jtulach/timing/boxes/StartGage02-Box_DsiplayCover_Part1.stl

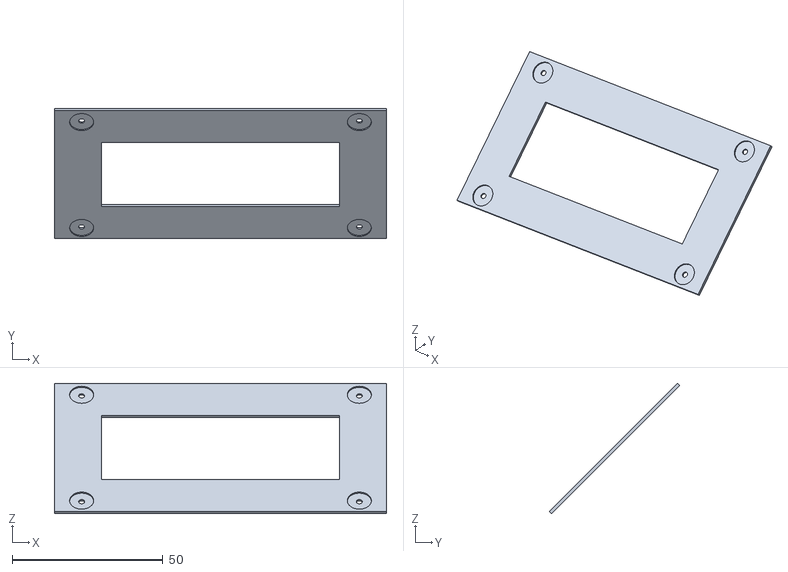
[picture p17: CAD file, 2019-12-12]
boxes/StartGage02-Box_DsiplayCover_Part1.stl
110.0 x 43.2 x 43.2
