jtulach/timing/boxes/krabickaSFotoTransistorem_04-Front1.stl

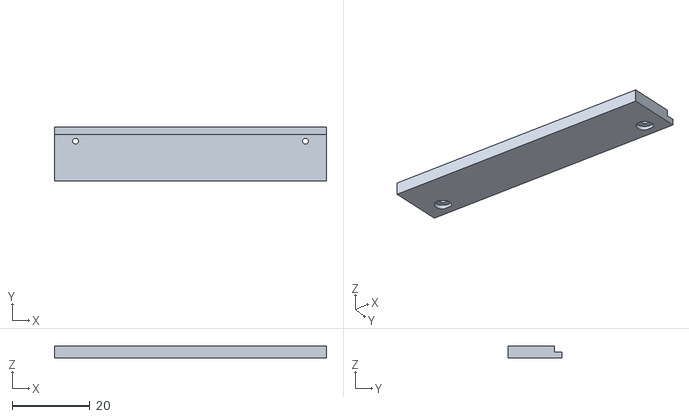
[picture p18: CAD file, 2019-12-12]
boxes/krabickaSFotoTransistorem_04-Front1.stl
70.0 x 14.0 x 3.00
