jtulach/timing/boxes/krabickaSFotoTransistorem_02-LaserHouse.stl

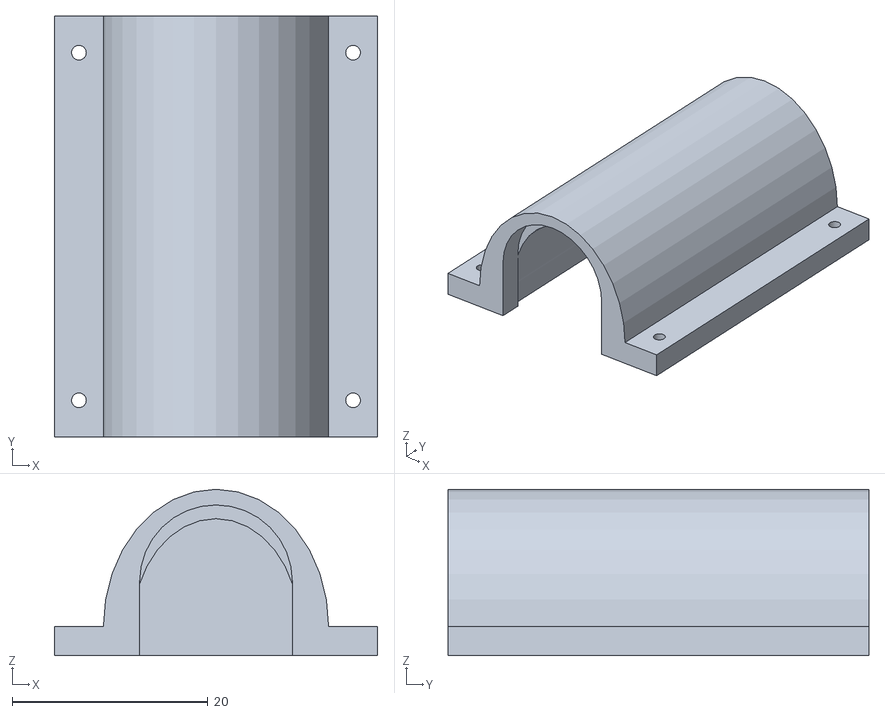
[picture p19: CAD file, 2019-12-12]
boxes/krabickaSFotoTransistorem_02-LaserHouse.stl
33.0 x 43.0 x 17.0
