jtulach/timing/boxes/krabickaSFotoTransistorem_04-Telescope_Part_2_Bottom.stl

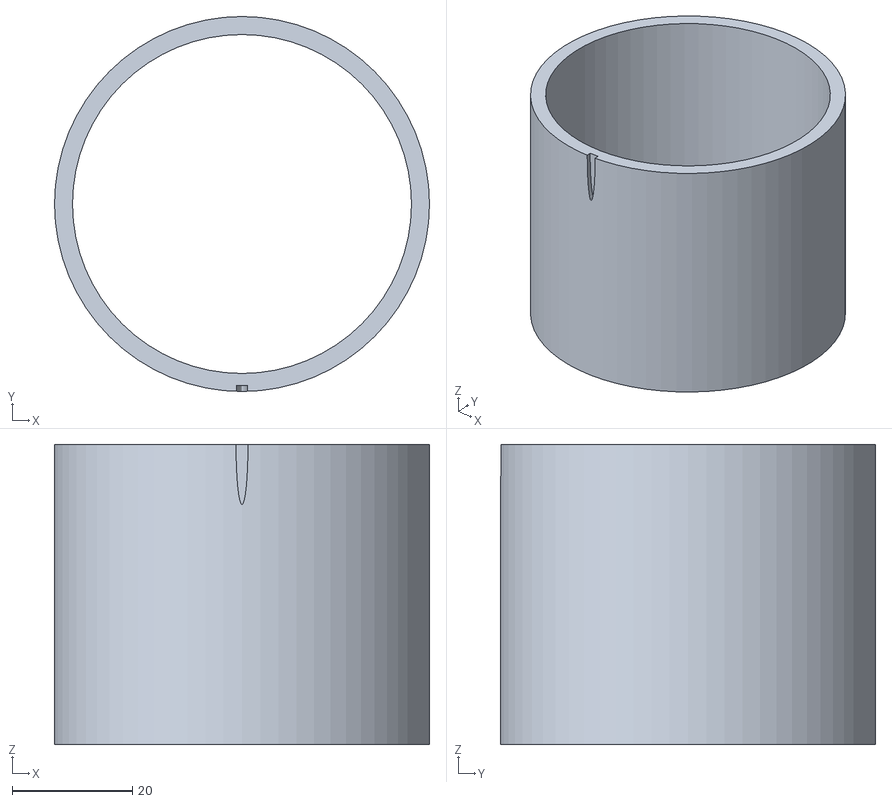
[picture p20: CAD file, 2019-12-12]
boxes/krabickaSFotoTransistorem_04-Telescope_Part_2_Bottom.stl
62.4 x 62.4 x 50.0
