jtulach/timing/boxes/krabickaSFotoTransistorem_04-Telescope_Part_5.stl

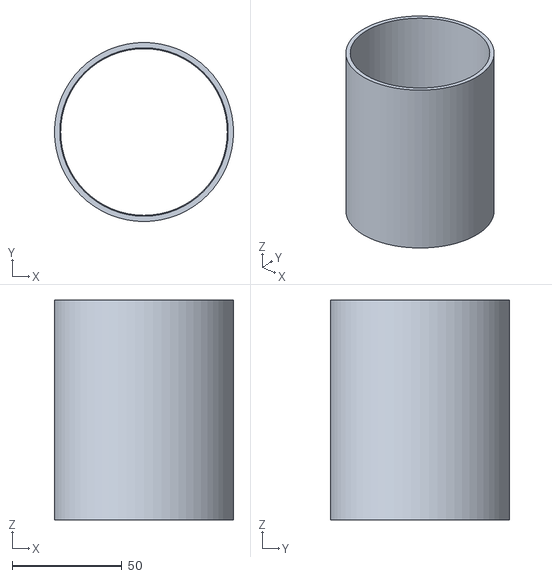
[picture p21: CAD file, 2019-12-12]
boxes/krabickaSFotoTransistorem_04-Telescope_Part_5.stl
81.4 x 81.4 x 100.0
