jtulach/timing/boxes/krabickaSFotoTransistorem_04-LaserBox_Right.stl

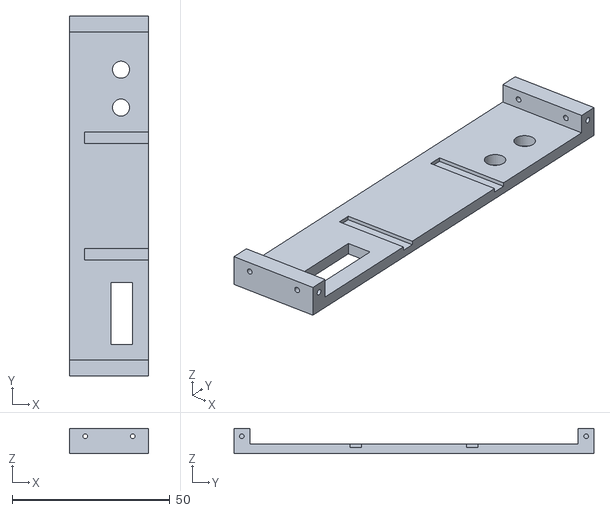
[picture p22: CAD file, 2019-12-12]
boxes/krabickaSFotoTransistorem_04-LaserBox_Right.stl
25.0 x 114.0 x 8.00
