jtulach/timing/boxes/StartGage02-RFISign.stl

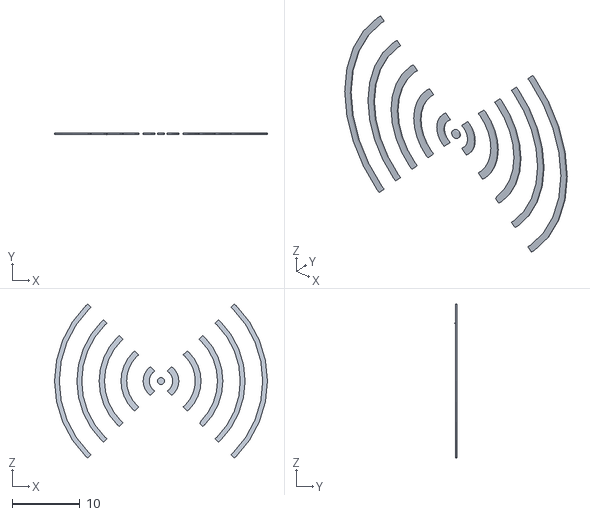
[picture p23: CAD file, 2019-12-12]
boxes/StartGage02-RFISign.stl
31.5 x 0.339 x 22.7
