jtulach/timing/boxes/StartGage02-Box_Back_Part1.stl

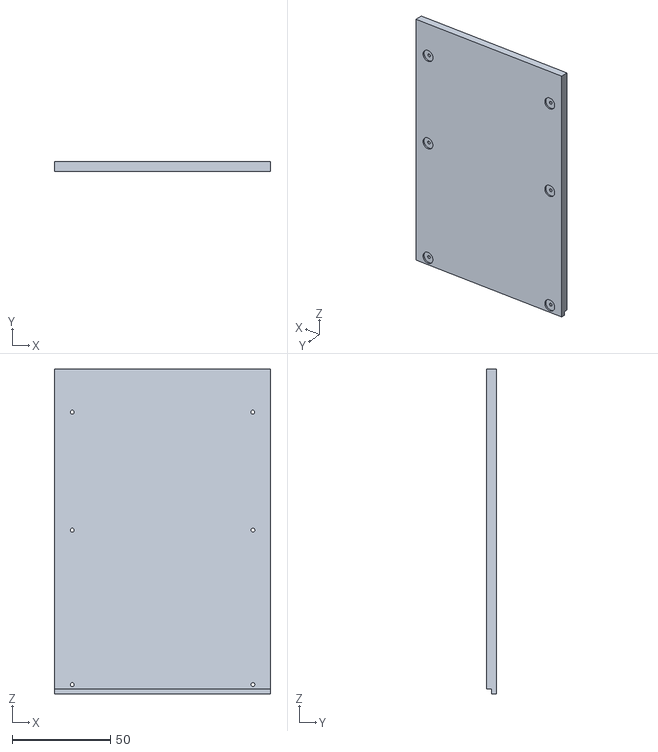
[picture p24: CAD file, 2019-12-12]
boxes/StartGage02-Box_Back_Part1.stl
110.0 x 5.00 x 165.5
