jtulach/timing/boxes/krabickaSFotoTransistorem_01-Bottom.stl

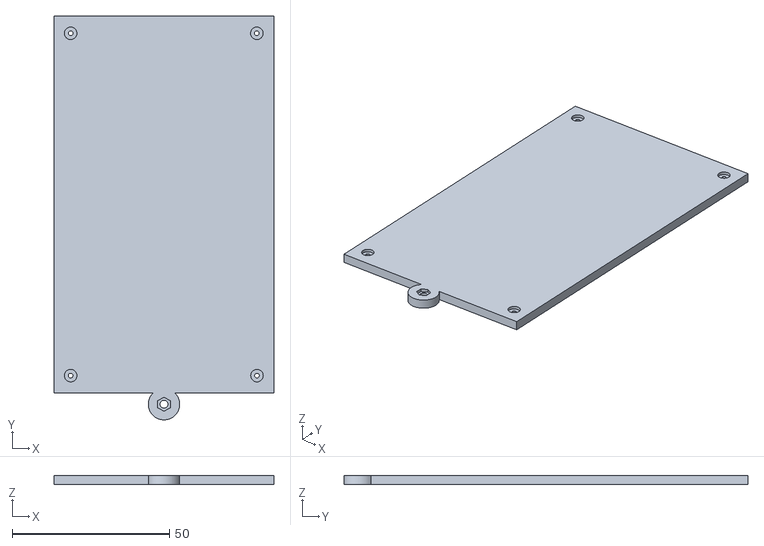
[picture p25: CAD file, 2019-12-12]
boxes/krabickaSFotoTransistorem_01-Bottom.stl
70.0 x 128.5 x 3.00
