jtulach/timing/boxes/krabickaSFotoTransistorem_02-Cylinder_055.stl

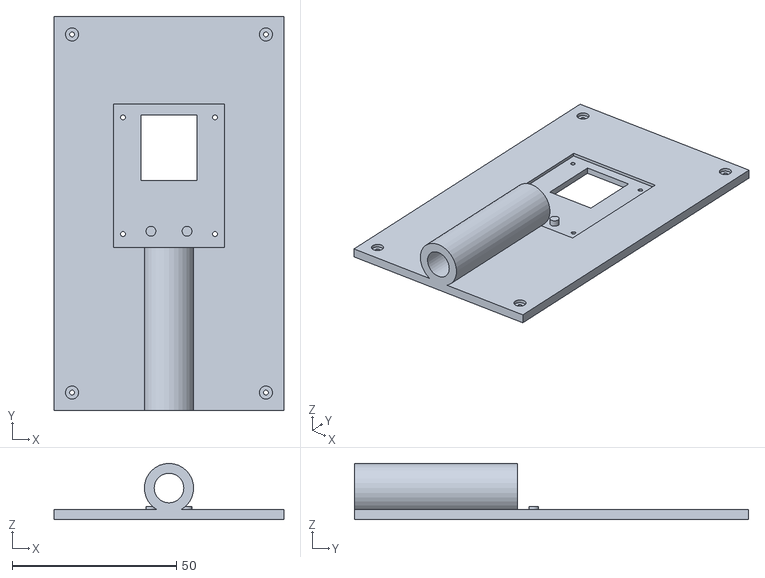
[picture p26: CAD file, 2019-12-12]
boxes/krabickaSFotoTransistorem_02-Cylinder_055.stl
70.0 x 120.0 x 17.1
