jtulach/timing/boxes/krabickaSFotoTransistorem_04-Telescope_Part_2_2.stl

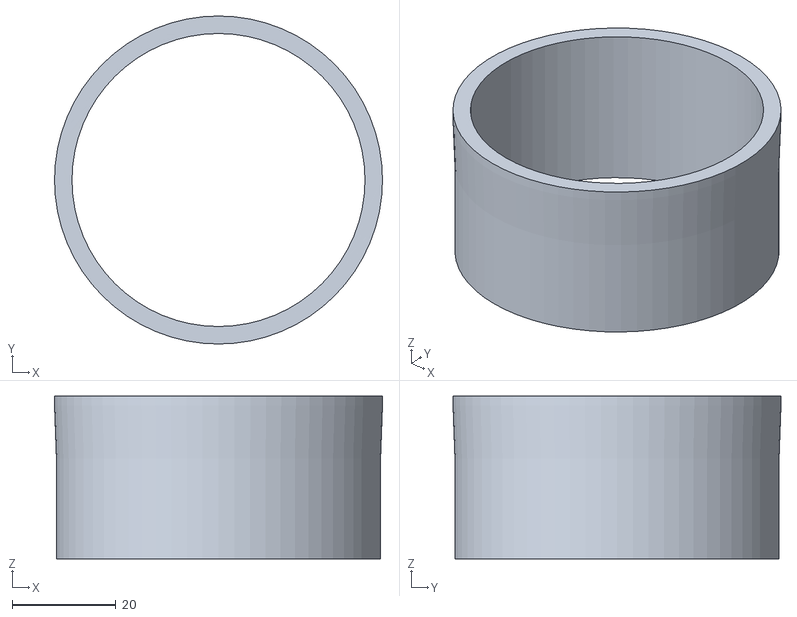
[picture p27: CAD file, 2019-12-12]
boxes/krabickaSFotoTransistorem_04-Telescope_Part_2_2.stl
63.1 x 63.1 x 31.3
