jtulach/timing/boxes/krabickaSFotoTransistorem_04-Telescope_Part_4_Bottom.stl

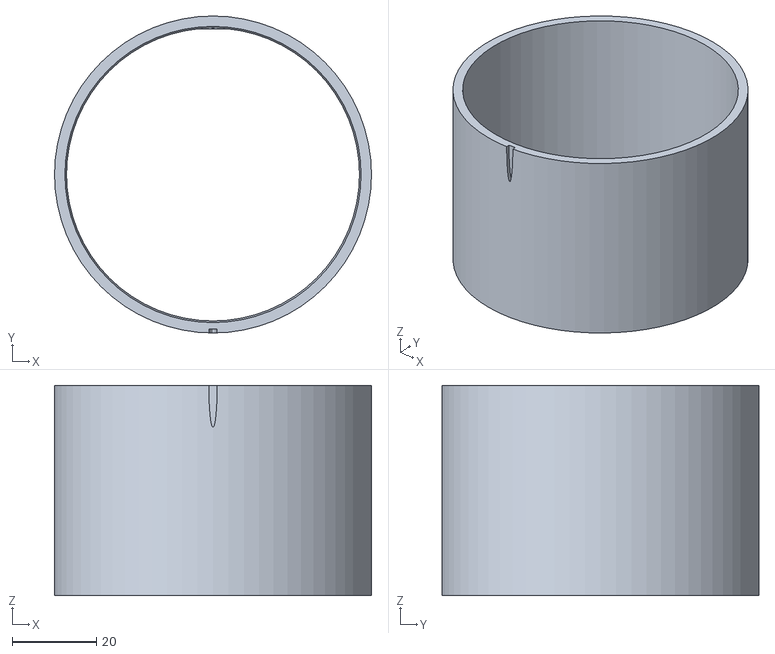
[picture p28: CAD file, 2019-12-12]
boxes/krabickaSFotoTransistorem_04-Telescope_Part_4_Bottom.stl
75.4 x 75.4 x 50.0
