jtulach/timing/boxes/StartGage-MicroSwitchHelper.stl

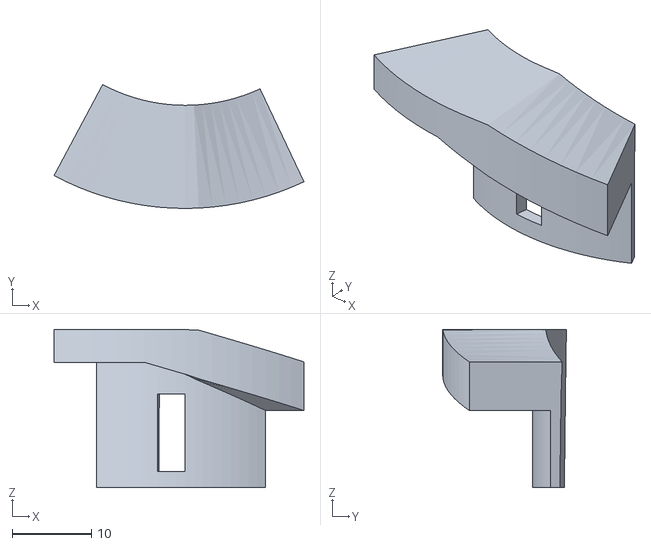
[picture p29: CAD file, 2019-12-12]
boxes/StartGage-MicroSwitchHelper.stl
31.5 x 15.6 x 19.9
