jtulach/timing/boxes/StartGage-LockCylinder.stl

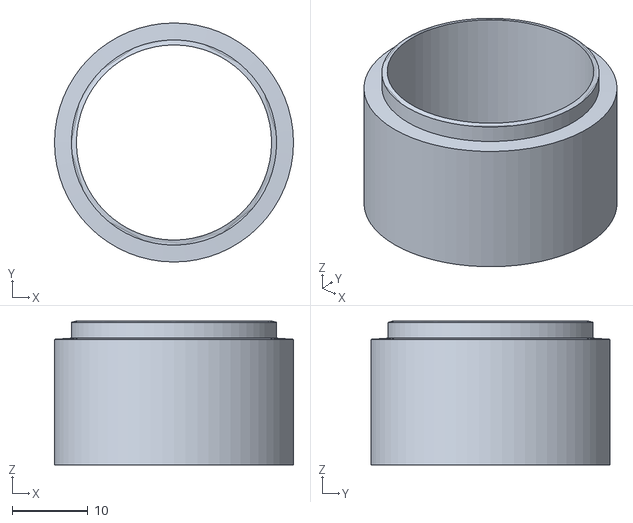
[picture p30: CAD file, 2019-12-12]
boxes/StartGage-LockCylinder.stl
31.5 x 31.5 x 19.0
