jtulach/timing/boxes/krabickaSFotoTransistorem_06-LaserBox-Top-3Lesers.stl

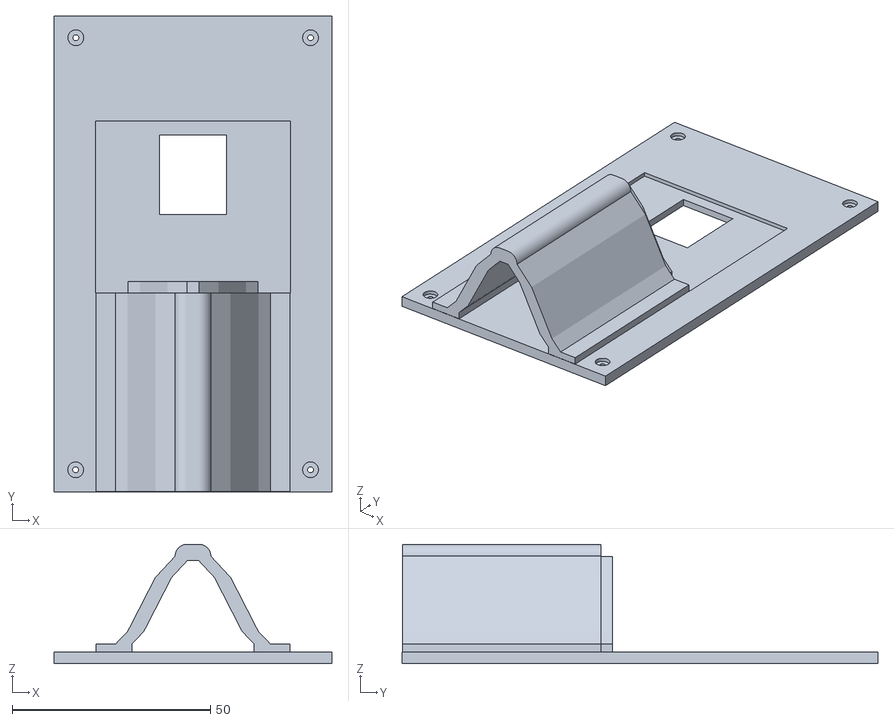
[picture p31: CAD file, 2019-12-12]
boxes/krabickaSFotoTransistorem_06-LaserBox-Top-3Lesers.stl
70.0 x 120.0 x 30.1
