jtulach/timing/boxes/krabickaSFotoTransistorem_04-FinisBox_DistanceForDiod.stl

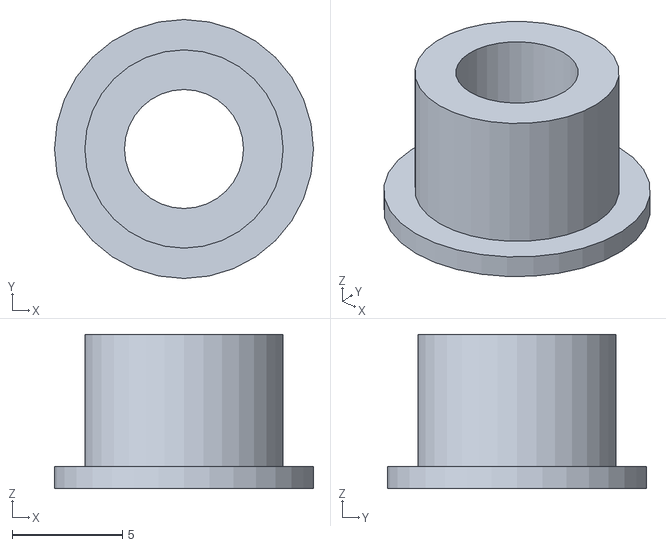
[picture p32: CAD file, 2019-12-12]
boxes/krabickaSFotoTransistorem_04-FinisBox_DistanceForDiod.stl
11.8 x 11.8 x 7.00
