jtulach/timing/boxes/krabickaSFotoTransistorem_04-LimitSwitch_DistancePad.stl

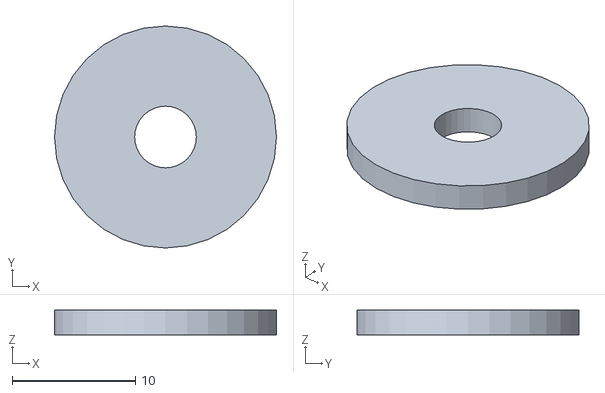
[picture p33: CAD file, 2019-12-12]
boxes/krabickaSFotoTransistorem_04-LimitSwitch_DistancePad.stl
18.0 x 18.0 x 2.00
