jtulach/timing/boxes/StartGage02-Box_DisplayCover_Part2.stl

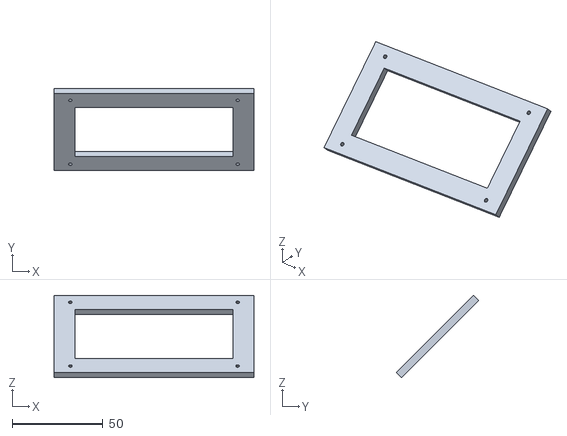
[picture p34: CAD file, 2019-12-12]
boxes/StartGage02-Box_DisplayCover_Part2.stl
110.0 x 45.3 x 45.3
