jtulach/timing/boxes/krabickaSFotoTransistorem_03-LeserBack.stl

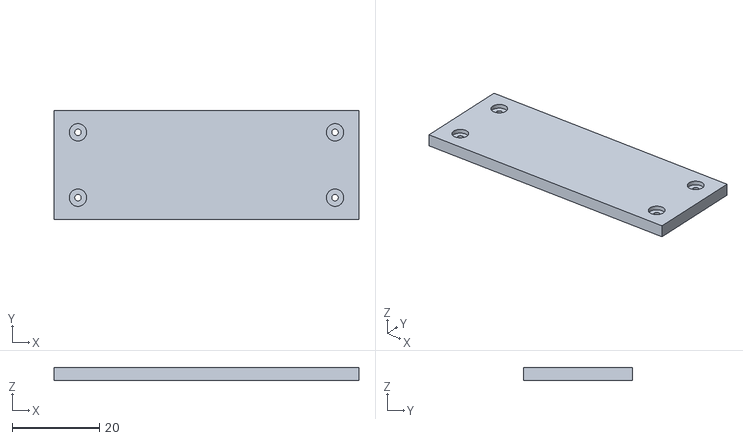
[picture p35: CAD file, 2019-12-12]
boxes/krabickaSFotoTransistorem_03-LeserBack.stl
70.0 x 25.0 x 3.00
