jtulach/timing/boxes/krabickaSFotoTransistorem_04-Telescope_Part_5_Bottom.stl

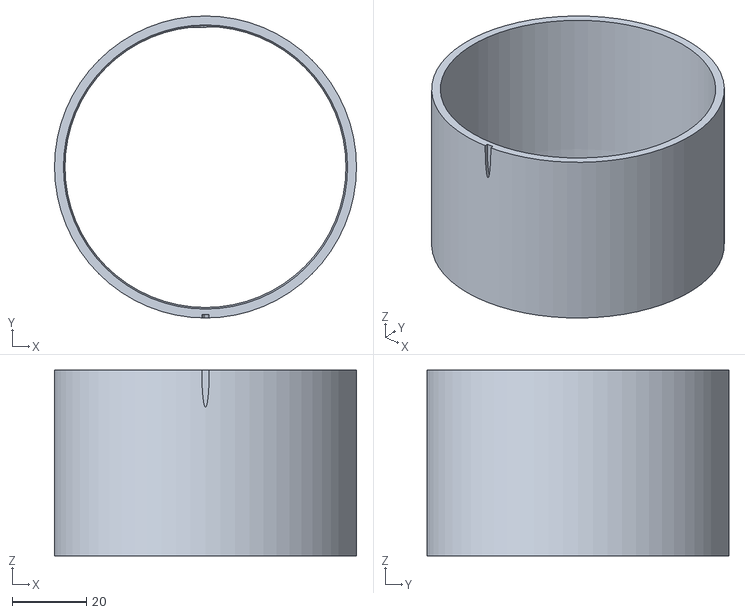
[picture p36: CAD file, 2019-12-12]
boxes/krabickaSFotoTransistorem_04-Telescope_Part_5_Bottom.stl
81.4 x 81.4 x 50.0
