jtulach/timing/boxes/krabickaSFotoTransistorem_01-PouzdraNaLaser.stl

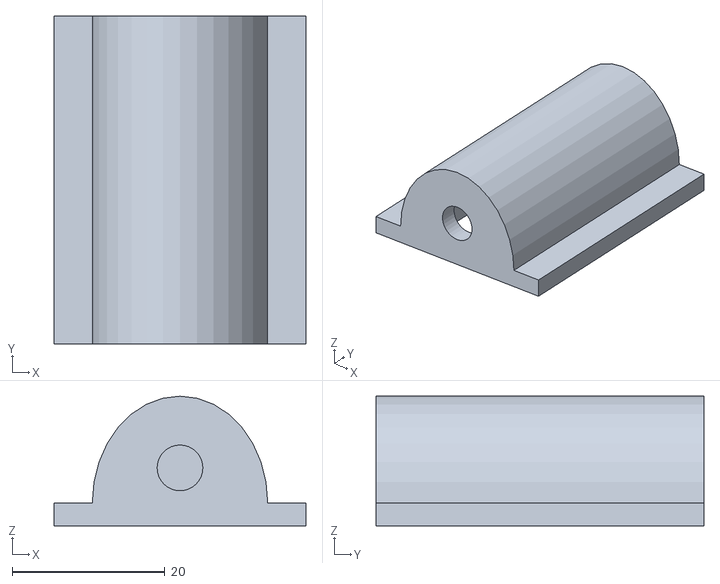
[picture p37: CAD file, 2019-12-12]
boxes/krabickaSFotoTransistorem_01-PouzdraNaLaser.stl
33.0 x 43.0 x 17.0
