jtulach/timing/boxes/krabickaSFotoTransistorem_01-Glass1.stl

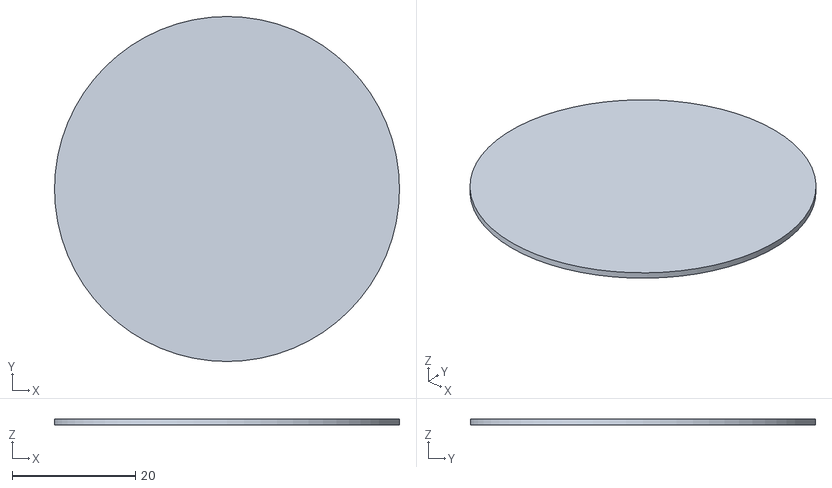
[picture p38: CAD file, 2019-12-12]
boxes/krabickaSFotoTransistorem_01-Glass1.stl
56.0 x 56.0 x 1.00
