jtulach/timing/boxes/StartGage02-Box_InnerHolderRight.stl

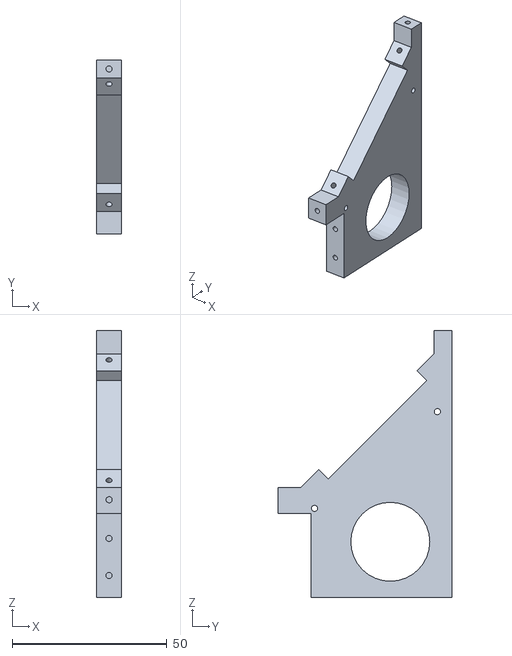
[picture p39: CAD file, 2019-12-12]
boxes/StartGage02-Box_InnerHolderRight.stl
8.00 x 56.3 x 86.3
