jtulach/timing/boxes/StartGage02-CasingTop.stl

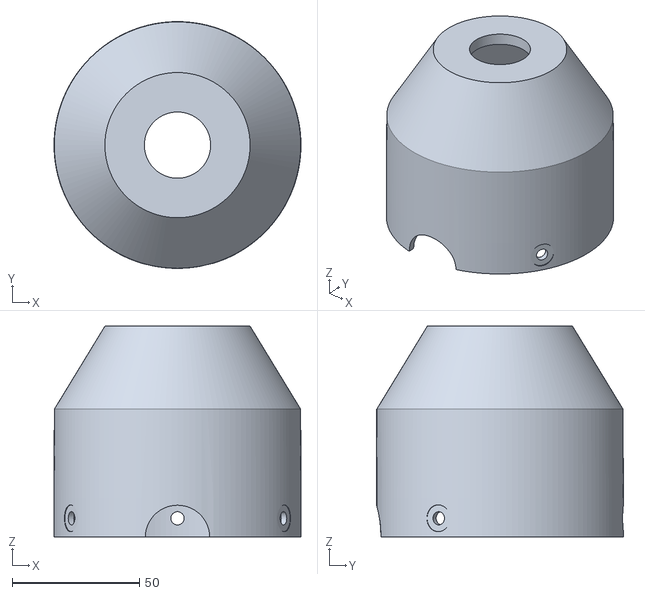
[picture p40: CAD file, 2019-12-12]
boxes/StartGage02-CasingTop.stl
97.0 x 96.9 x 82.8
