jtulach/timing/boxes/krabickaSFotoTransistorem_04-Telescope_Part_4.stl

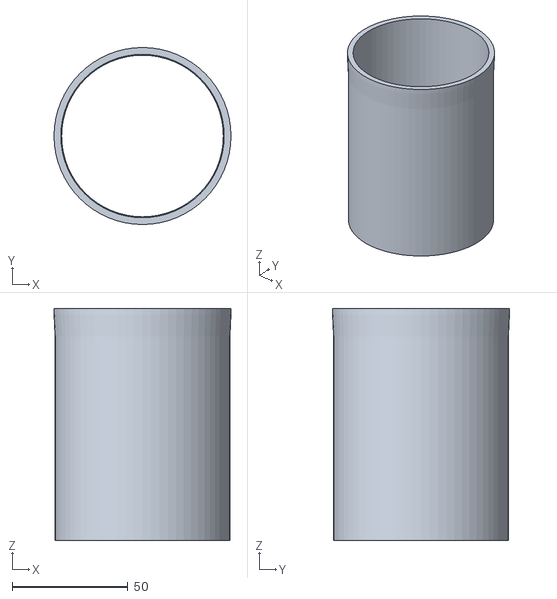
[picture p41: CAD file, 2019-12-12]
boxes/krabickaSFotoTransistorem_04-Telescope_Part_4.stl
76.3 x 76.3 x 100.0
