jtulach/timing/boxes/krabickaSFotoTransistorem_01-Glass.stl

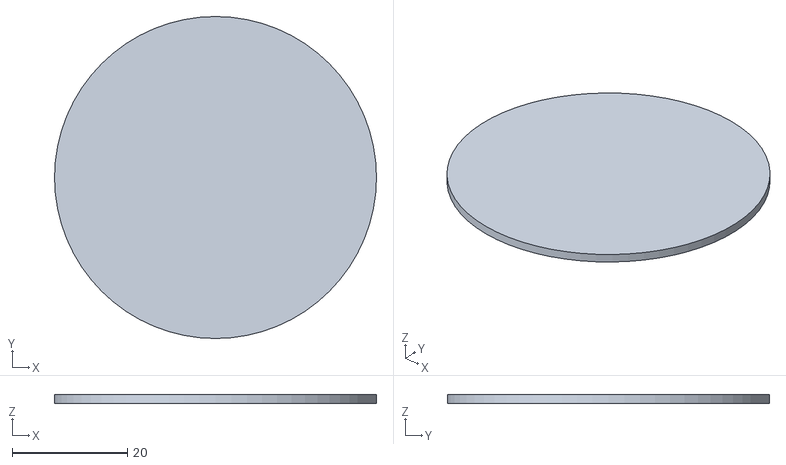
[picture p42: CAD file, 2019-12-12]
boxes/krabickaSFotoTransistorem_01-Glass.stl
56.0 x 56.0 x 1.50
