jtulach/timing/boxes/StartGage02-Box_Front_Part2.stl

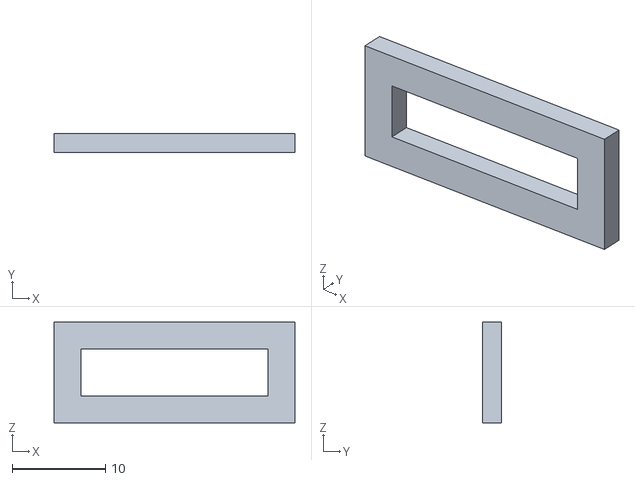
[picture p43: CAD file, 2019-12-12]
boxes/StartGage02-Box_Front_Part2.stl
25.8 x 2.00 x 10.8
