jtulach/timing/boxes/LaserBox-LaserBox-3LaserCaver.stl

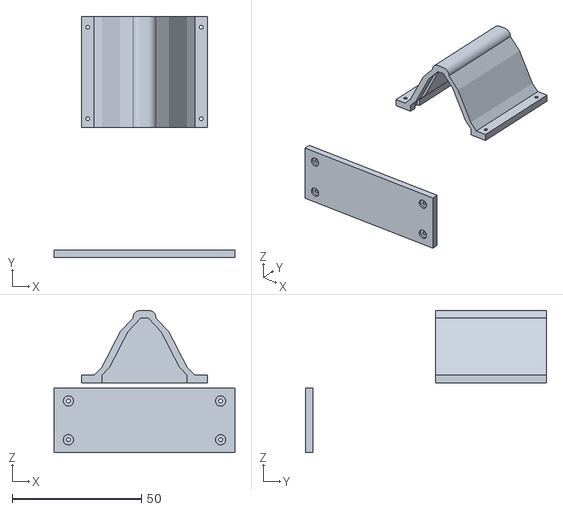
[picture p44: CAD file, 2019-12-12]
boxes/LaserBox-LaserBox-3LaserCaver.stl
70.0 x 93.4 x 55.1
