jtulach/timing/boxes/krabickaSFotoTransistorem_06-LaserBox-3Leser-Top.stl

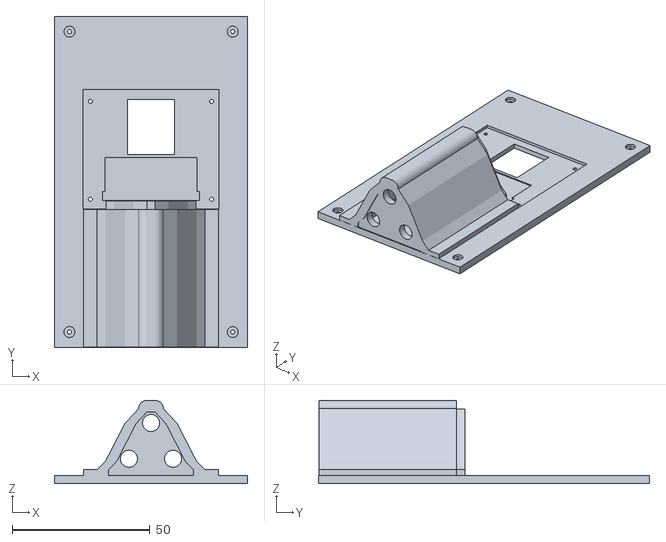
[picture p45: CAD file, 2019-12-12]
boxes/krabickaSFotoTransistorem_06-LaserBox-3Leser-Top.stl
70.0 x 120.0 x 30.1
