jtulach/timing/boxes/krabickaSFotoTransistorem_03-LaseFront2.stl

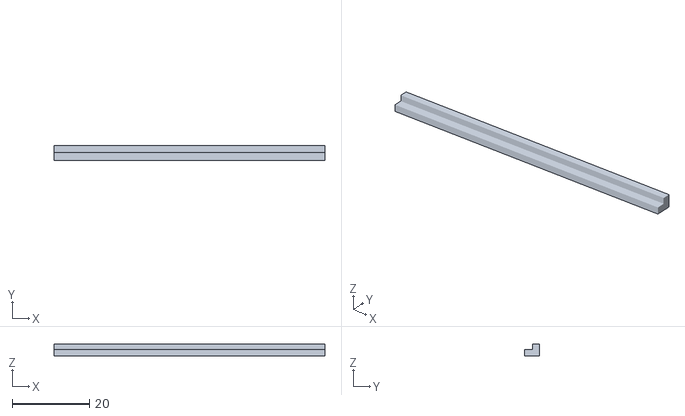
[picture p46: CAD file, 2019-12-12]
boxes/krabickaSFotoTransistorem_03-LaseFront2.stl
70.0 x 3.78 x 3.00
