jtulach/timing/boxes/krabickaSFotoTransistorem_01-Top.stl

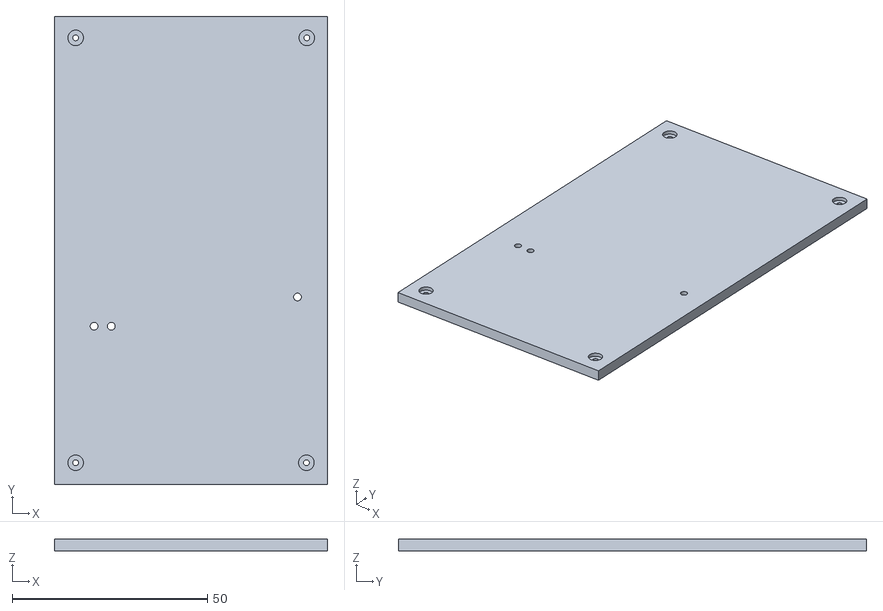
[picture p47: CAD file, 2019-12-12]
boxes/krabickaSFotoTransistorem_01-Top.stl
70.0 x 120.0 x 3.00
