jtulach/timing/boxes/StartGage02-Box_Right.stl

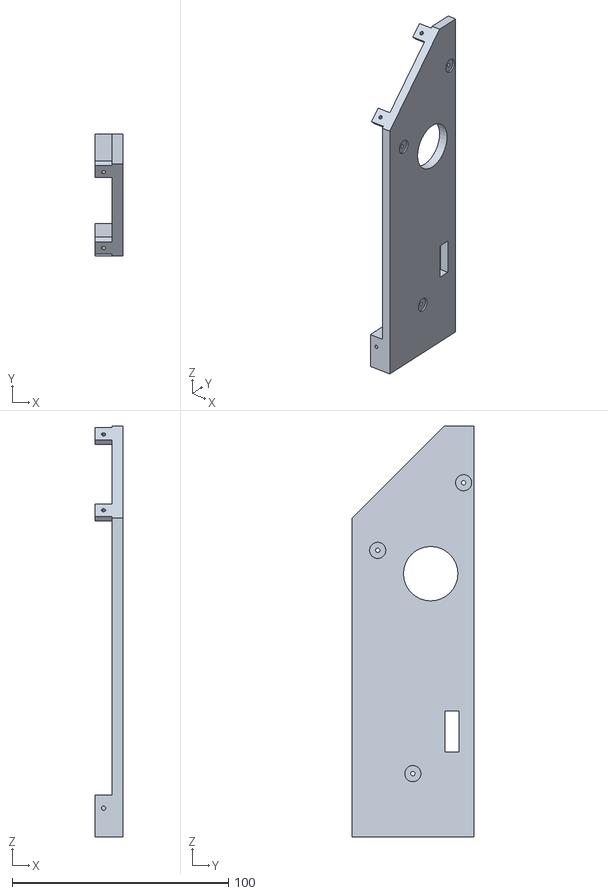
[picture p48: CAD file, 2019-12-12]
boxes/StartGage02-Box_Right.stl
13.0 x 56.3 x 190.0
