jtulach/timing/boxes/krabickaSFotoTransistorem_04-StartBox_Front_Part1.stl

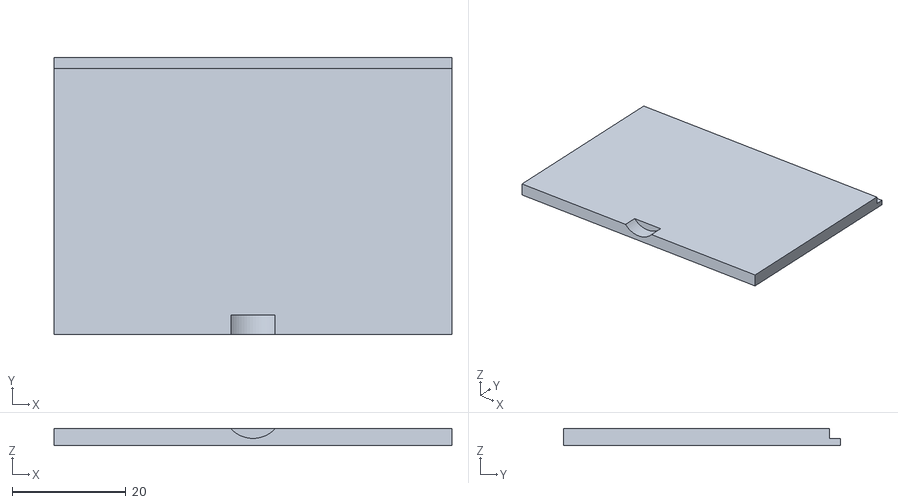
[picture p49: CAD file, 2019-12-12]
boxes/krabickaSFotoTransistorem_04-StartBox_Front_Part1.stl
70.0 x 48.8 x 3.00
