jtulach/timing/boxes/krabickaSFotoTransistorem_04-Telescope_Part_3_Top.stl

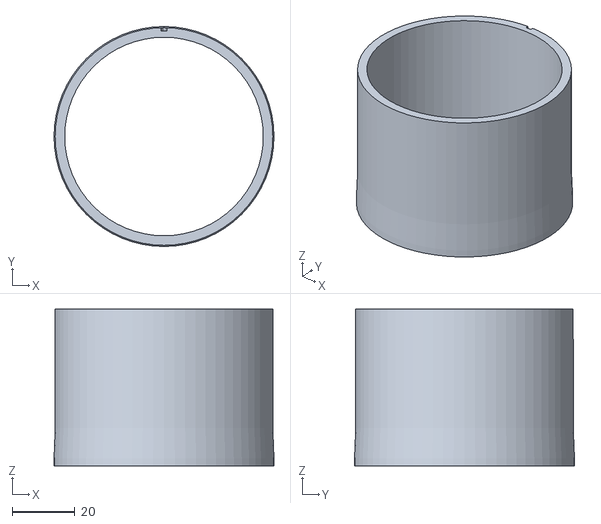
[picture p50: CAD file, 2019-12-12]
boxes/krabickaSFotoTransistorem_04-Telescope_Part_3_Top.stl
70.2 x 70.2 x 50.0
