jtulach/timing/boxes/krabickaSFotoTransistorem_01-Beck.stl

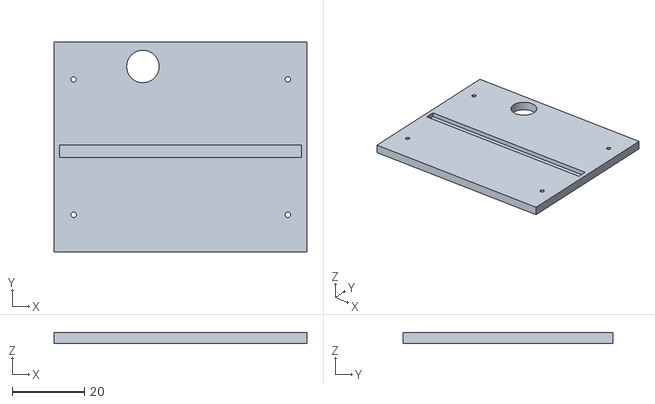
[picture p51: CAD file, 2019-12-12]
boxes/krabickaSFotoTransistorem_01-Beck.stl
70.0 x 58.0 x 3.00
