jtulach/timing/boxes/StartGage-LockPlankWithHole.stl

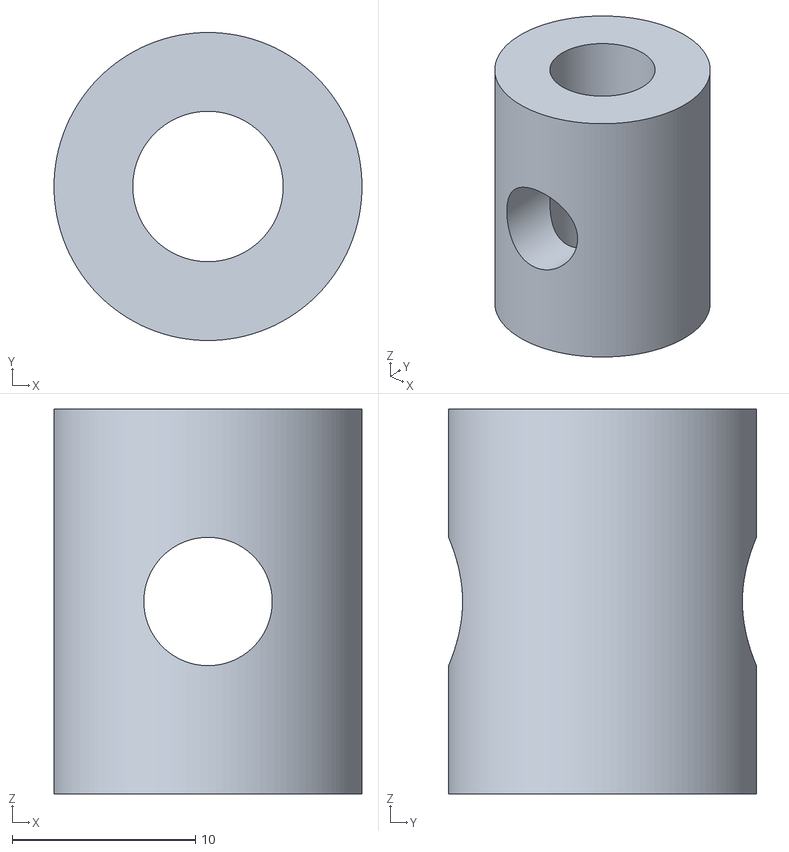
[picture p52: CAD file, 2019-12-12]
boxes/StartGage-LockPlankWithHole.stl
16.8 x 16.8 x 21.0
