jtulach/timing/boxes/krabickaSFotoTransistorem_01-DeskaProstredni_001.stl

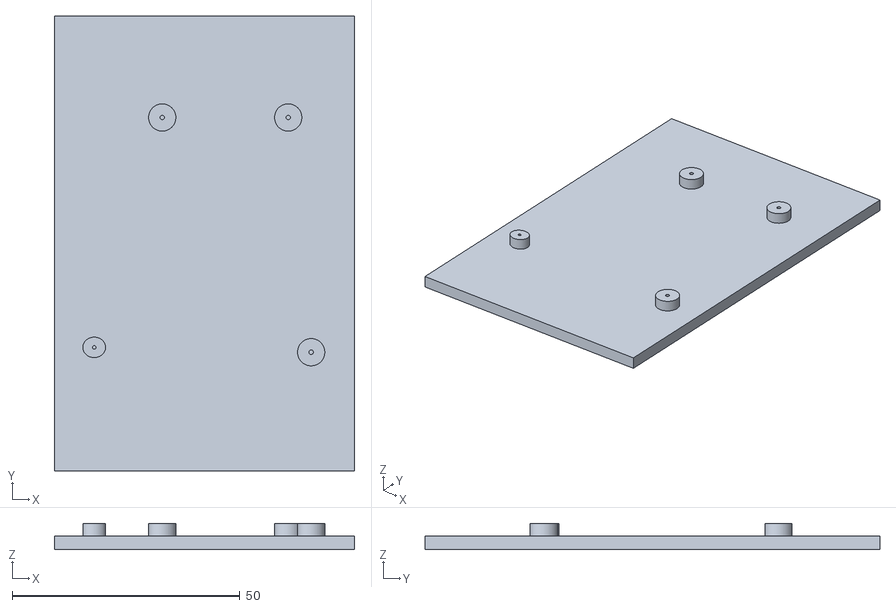
[picture p53: CAD file, 2019-12-12]
boxes/krabickaSFotoTransistorem_01-DeskaProstredni_001.stl
66.0 x 100.0 x 5.76
