jtulach/timing/boxes/StartGage02-ArduinoBase.stl

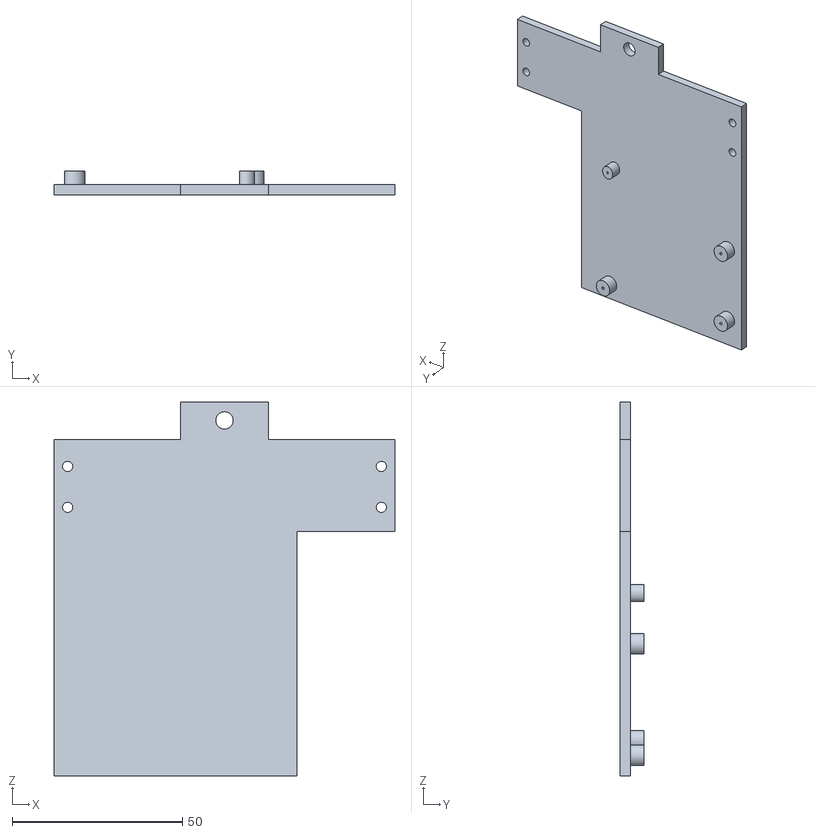
[picture p54: CAD file, 2019-12-12]
boxes/StartGage02-ArduinoBase.stl
100.0 x 7.00 x 109.7
