jtulach/timing/boxes/krabickaSFotoTransistorem_03-LaserFront1.stl

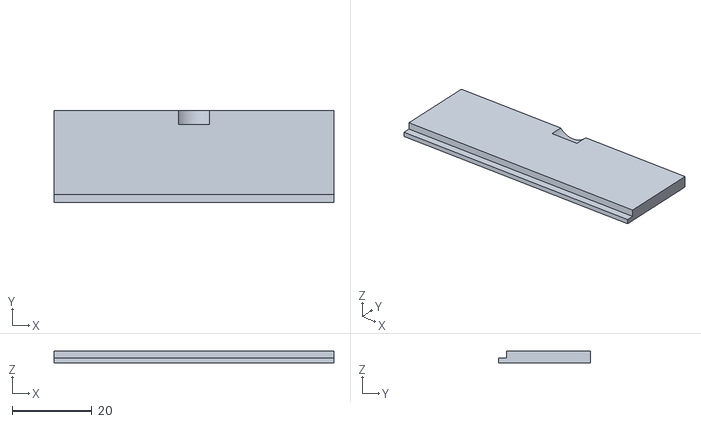
[picture p55: CAD file, 2019-12-12]
boxes/krabickaSFotoTransistorem_03-LaserFront1.stl
70.0 x 23.0 x 3.00
