jtulach/timing/boxes/StartGage02-Box_Bottom.stl

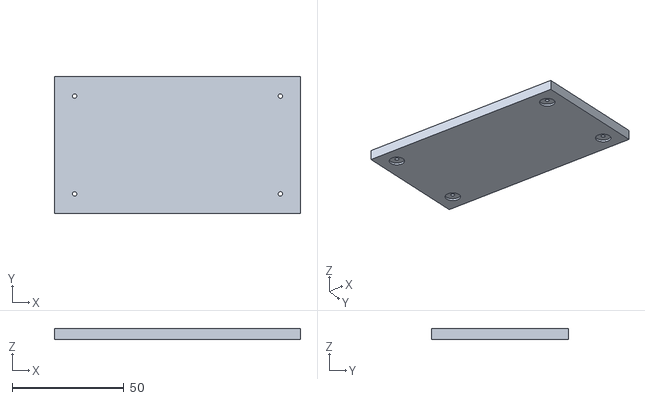
[picture p56: CAD file, 2019-12-12]
boxes/StartGage02-Box_Bottom.stl
110.0 x 61.3 x 5.00
