jtulach/timing/boxes/krabickaSFotoTransistorem_03-Back_Start.stl

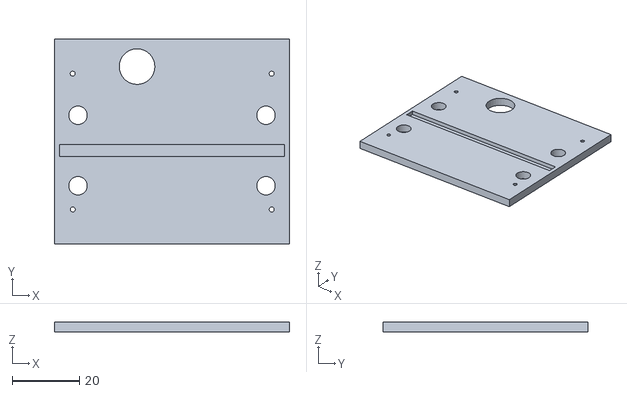
[picture p57: CAD file, 2019-12-12]
boxes/krabickaSFotoTransistorem_03-Back_Start.stl
70.0 x 61.0 x 3.00
