jtulach/timing/boxes/StartGage02-Box_Back_Part2.stl

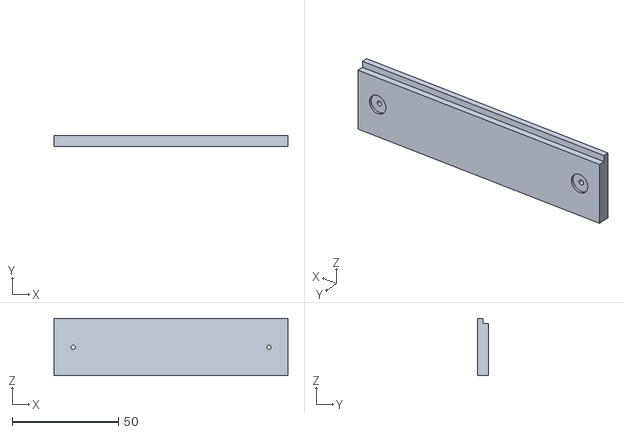
[picture p58: CAD file, 2019-12-12]
boxes/StartGage02-Box_Back_Part2.stl
110.0 x 5.00 x 26.9
