jtulach/timing/boxes/krabickaSFotoTransistorem_03-Front2.stl

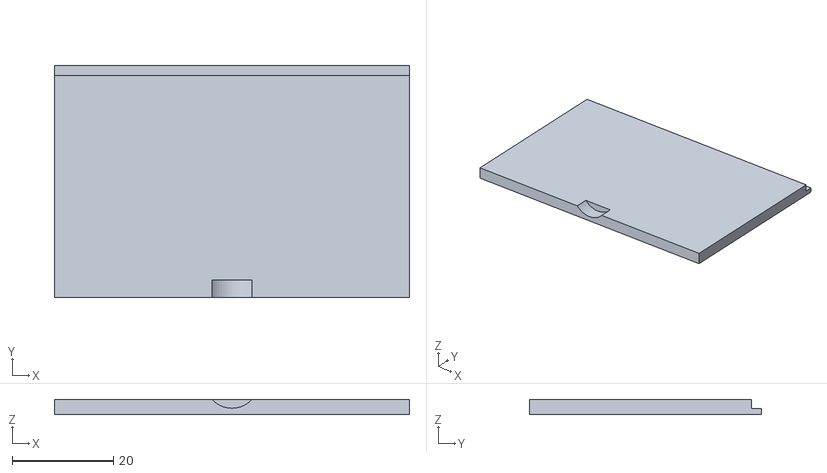
[picture p59: CAD file, 2019-12-12]
boxes/krabickaSFotoTransistorem_03-Front2.stl
70.0 x 45.8 x 3.00
