jtulach/timing/boxes/krabickaSFotoTransistorem_04-Telescope_Part_4_Top.stl

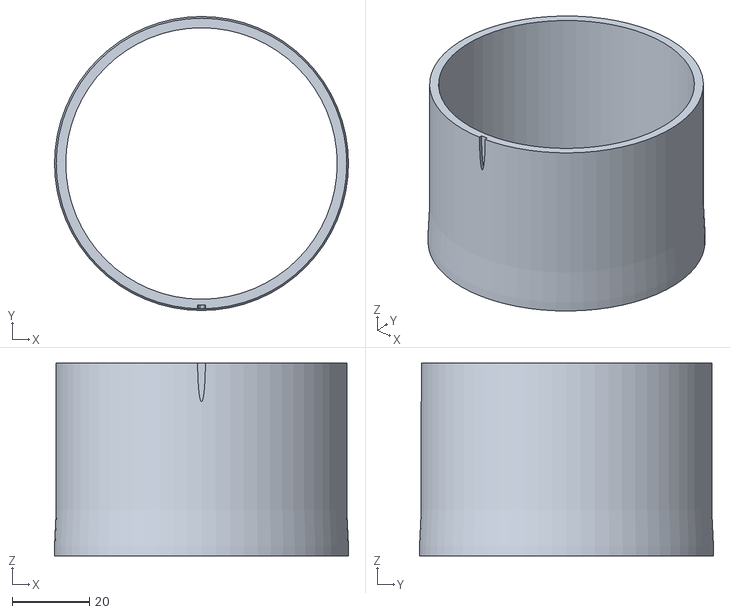
[picture p60: CAD file, 2019-12-12]
boxes/krabickaSFotoTransistorem_04-Telescope_Part_4_Top.stl
76.3 x 76.3 x 50.0
