jtulach/timing/boxes/krabickaSFotoTransistorem_03-LaserLeft.stl

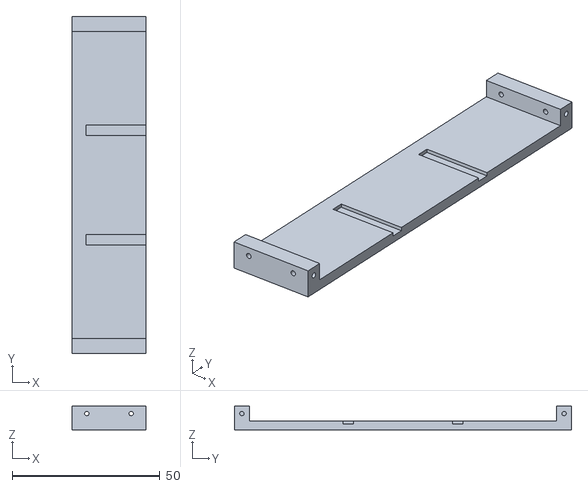
[picture p61: CAD file, 2019-12-12]
boxes/krabickaSFotoTransistorem_03-LaserLeft.stl
25.0 x 114.0 x 8.00
