jtulach/timing/boxes/krabickaSFotoTransistorem_04-Telescope_Part_1.stl

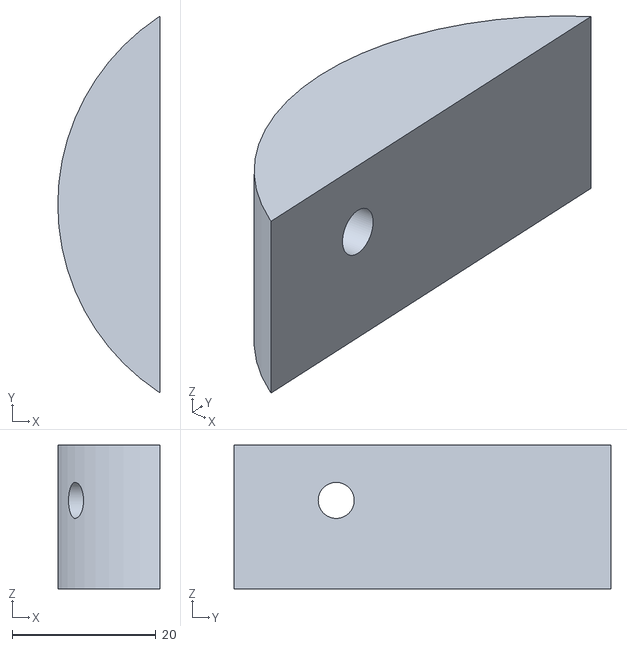
[picture p62: CAD file, 2019-12-12]
boxes/krabickaSFotoTransistorem_04-Telescope_Part_1.stl
14.2 x 52.3 x 20.0
