jtulach/timing/boxes/StartGage02-Box_LeftHolder_Part2.stl

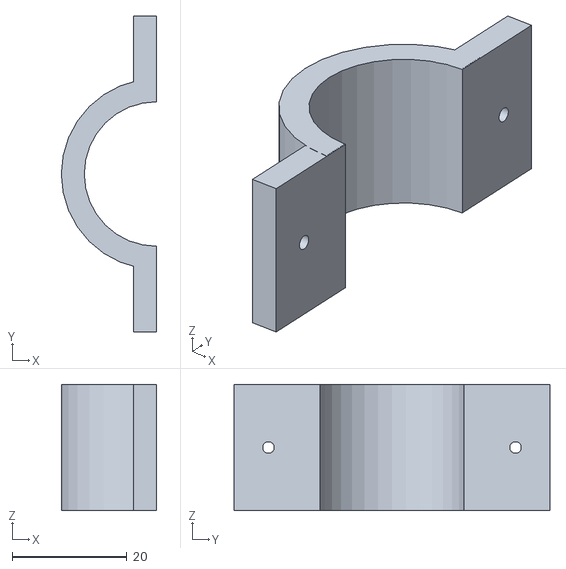
[picture p63: CAD file, 2019-12-12]
boxes/StartGage02-Box_LeftHolder_Part2.stl
16.6 x 55.0 x 22.0
