jtulach/timing/boxes/StartGage02-Box_Middle.stl

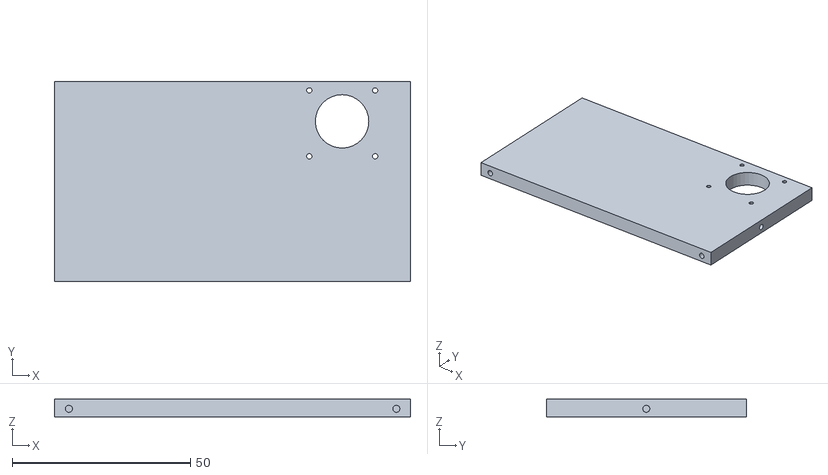
[picture p64: CAD file, 2019-12-12]
boxes/StartGage02-Box_Middle.stl
100.0 x 56.3 x 5.00
