jtulach/timing/boxes/krabickaSFotoTransistorem_01-Hook.stl

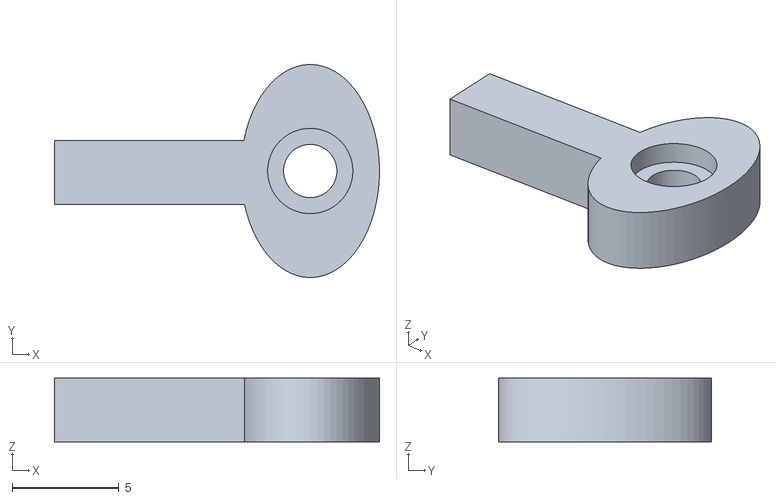
[picture p65: CAD file, 2019-12-12]
boxes/krabickaSFotoTransistorem_01-Hook.stl
15.2 x 10.0 x 3.00
