jtulach/timing/boxes/krabickaSFotoTransistorem_04-Telescope_Part_3_2.stl

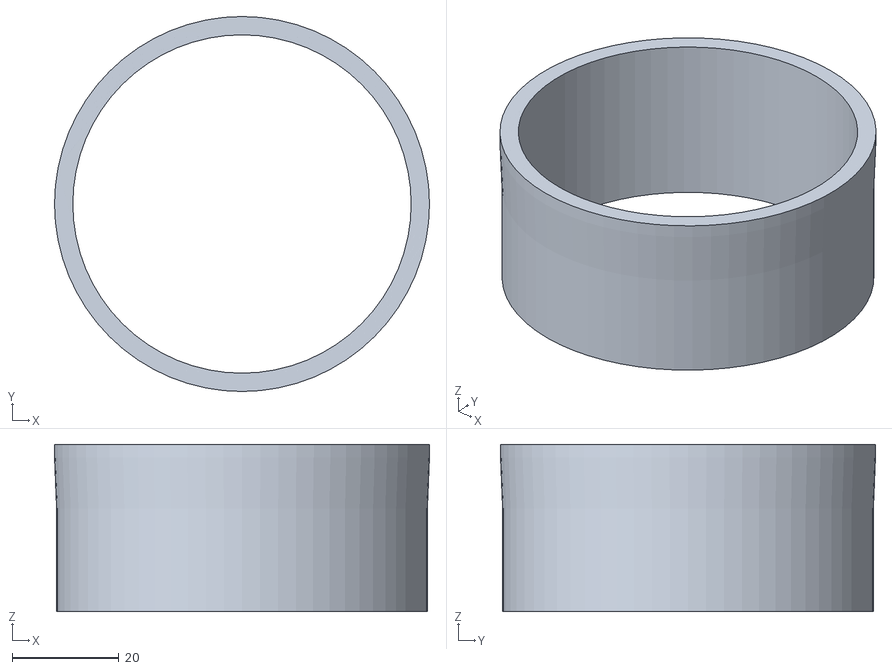
[picture p66: CAD file, 2019-12-12]
boxes/krabickaSFotoTransistorem_04-Telescope_Part_3_2.stl
70.2 x 70.2 x 31.3
