jtulach/timing/boxes/krabickaSFotoTransistorem_04-Telescope_Part_3.stl

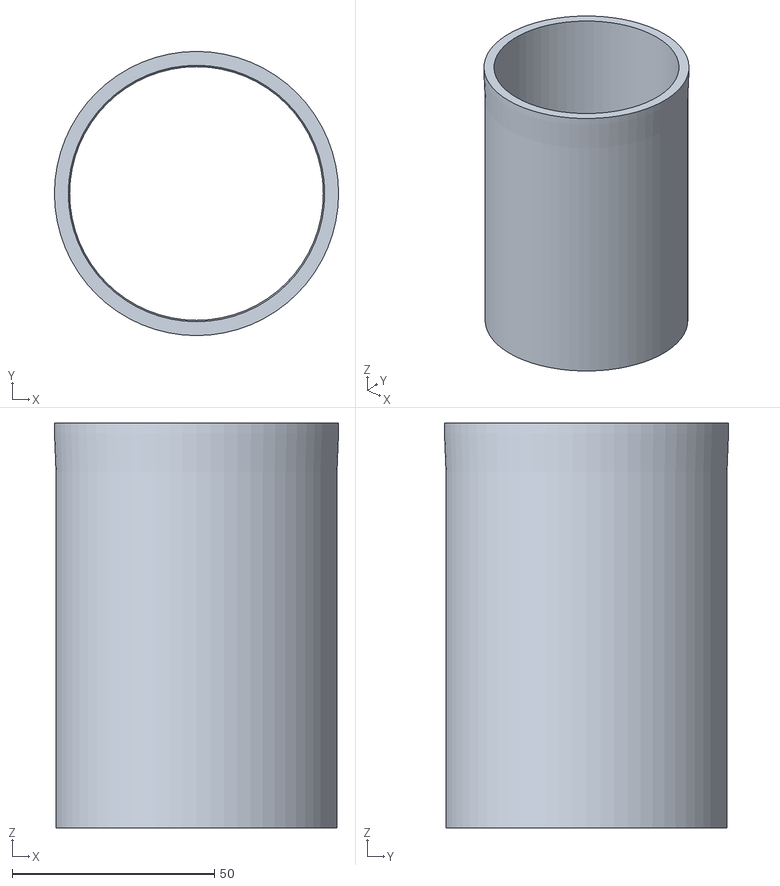
[picture p67: CAD file, 2019-12-12]
boxes/krabickaSFotoTransistorem_04-Telescope_Part_3.stl
70.2 x 70.2 x 100.0
