jtulach/timing/boxes/StartGage02-Box_DisplayCover_Part3.stl

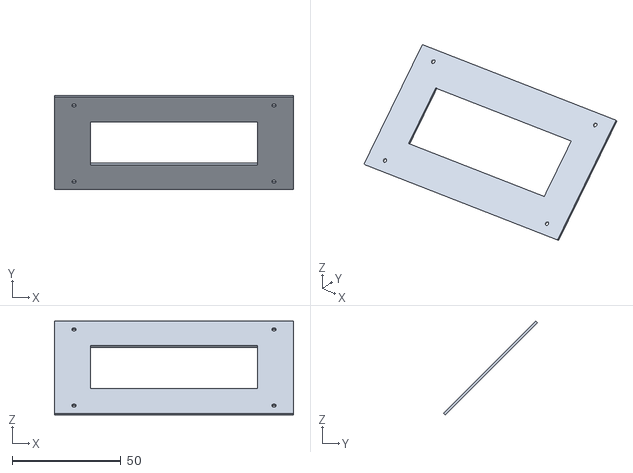
[picture p68: CAD file, 2019-12-12]
boxes/StartGage02-Box_DisplayCover_Part3.stl
110.0 x 43.1 x 43.1
