jtulach/timing/boxes/StartGage02-CasingBottom.stl

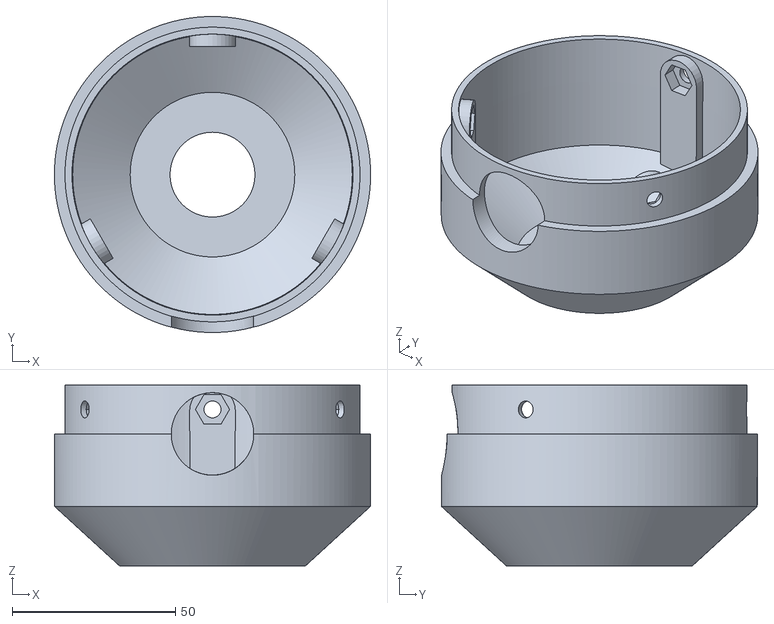
[picture p69: CAD file, 2019-12-12]
boxes/StartGage02-CasingBottom.stl
97.0 x 96.9 x 55.5
