jtulach/timing/boxes/krabickaSFotoTransistorem_04-Telescope_Part_3_Bottom.stl

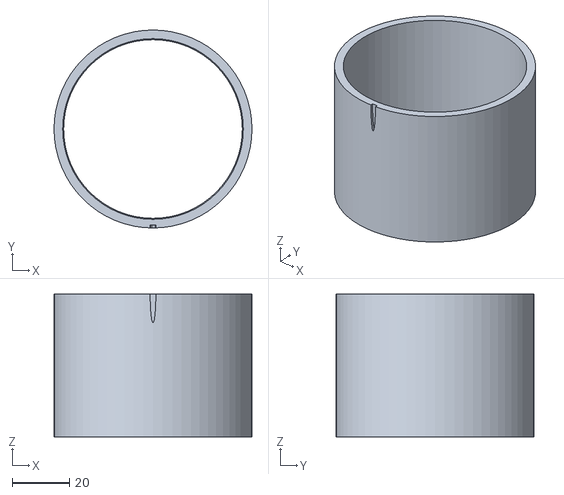
[picture p71: CAD file, 2019-12-12]
boxes/krabickaSFotoTransistorem_04-Telescope_Part_3_Bottom.stl
69.4 x 69.4 x 50.0
