jtulach/timing/boxes/krabickaSFotoTransistorem_01-Trap.stl

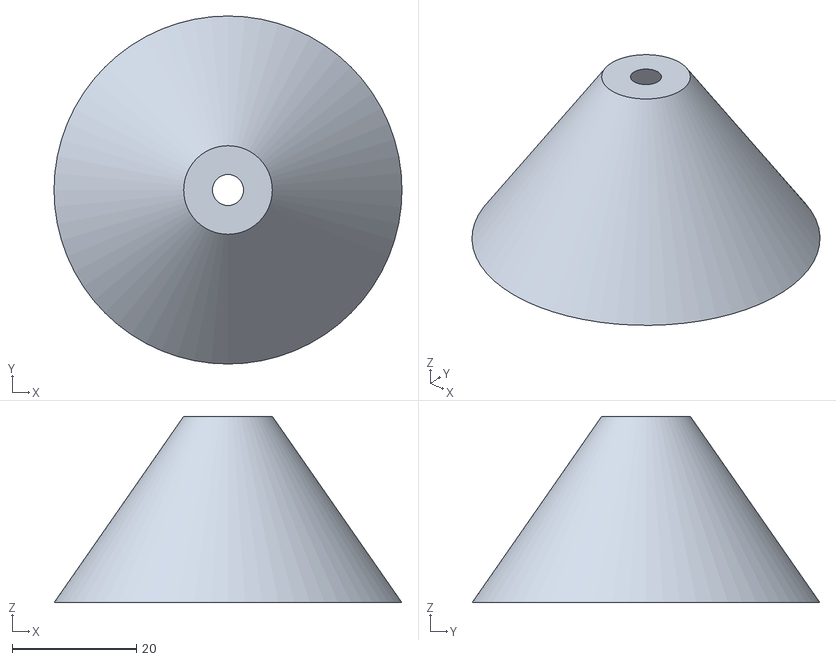
[picture p72: CAD file, 2019-12-12]
boxes/krabickaSFotoTransistorem_01-Trap.stl
56.0 x 56.0 x 30.0
