jtulach/timing/boxes/krabickaSFotoTransistorem_04-Telescope_Part_2_Top.stl

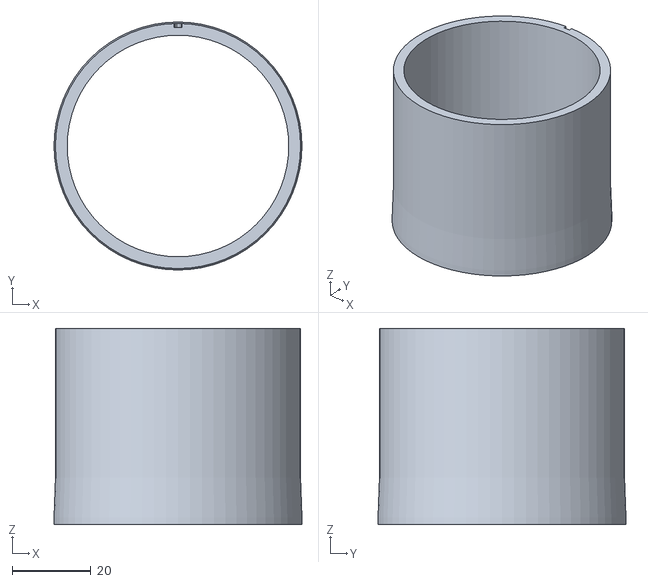
[picture p73: CAD file, 2019-12-12]
boxes/krabickaSFotoTransistorem_04-Telescope_Part_2_Top.stl
63.1 x 63.1 x 50.0
