jtulach/timing/boxes/krabickaSFotoTransistorem_06-RingInTelescope.stl

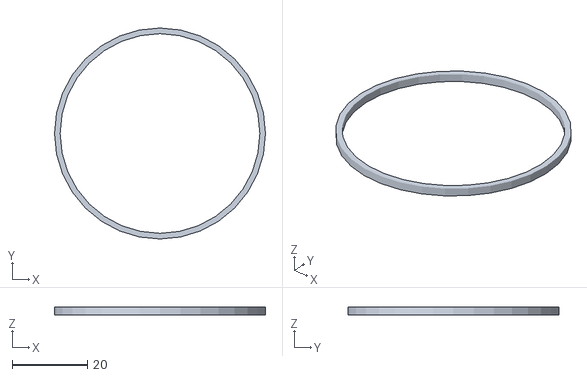
[picture p74: CAD file, 2019-12-12]
boxes/krabickaSFotoTransistorem_06-RingInTelescope.stl
56.0 x 56.0 x 2.00
