jtulach/timing/boxes/StartGage02-Box_Top.stl

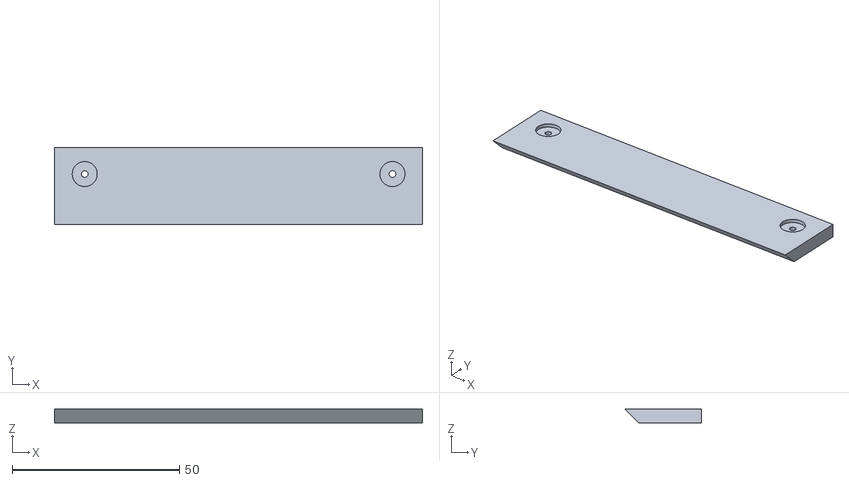
[picture p75: CAD file, 2019-12-12]
boxes/StartGage02-Box_Top.stl
110.0 x 23.0 x 4.25
