jtulach/timing/boxes/StartGage02-Box_LeftHolder_Part1.stl

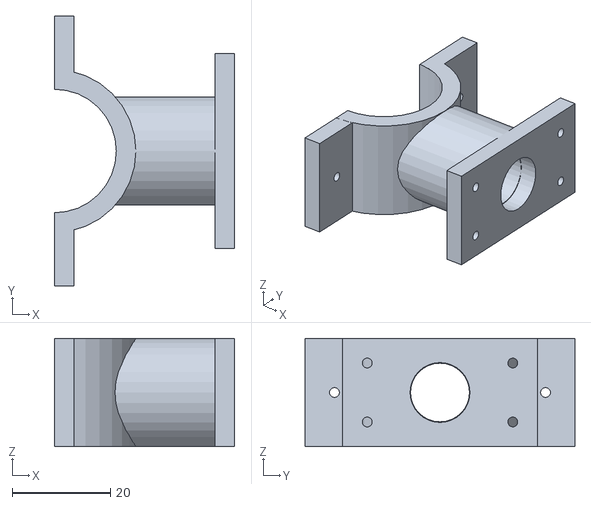
[picture p76: CAD file, 2019-12-12]
boxes/StartGage02-Box_LeftHolder_Part1.stl
36.7 x 55.0 x 22.0
