jtulach/timing/java/server/src/main/java/org/apidesign/gate/timing/server/Main.java

package org.apidesign.gate.timing.server;

import java.io.File;
import java.io.IOException;
import java.net.Inet4Address;
import java.net.InterfaceAddress;
import java.net.NetworkInterface;
import java.net.URI;
import java.util.Enumeration;
import java.util.logging.ConsoleHandler;
import java.util.logging.Level;
import java.util.logging.Logger;
import javax.ws.rs.container.ContainerRequestContext;
import javax.ws.rs.container.ContainerResponseContext;
import javax.ws.rs.container.ContainerResponseFilter;
import org.apidesign.gate.timing.shared.Settings;
import org.glassfish.grizzly.http.server.HttpServer;
import org.glassfish.hk2.utilities.binding.AbstractBinder;
import org.glassfish.jersey.grizzly2.httpserver.GrizzlyHttpServerFactory;
import org.glassfish.jersey.server.ResourceConfig;

/** Starts REST server based on Jersey.
 */
final class Main implements ContainerResponseFilter {
    static final Logger LOG = Logger.getLogger("org.apidesign.gate.timing.server");

    public static void main(String... args) throws Exception {
        int port = 8080;
        if (args.length >= 1) {
            port = Integer.parseInt(args[0]);
        }
        URI u = new URI("http://0.0.0.0:" + port + "/");

        File dir;
        if (args.length >= 2) {
            dir = new File(args[1]);
            dir.mkdirs();
        } else {
            dir = null;
        }

        turnLoggingOn();

        HttpServer server = createServer(u, dir);
        System.err.println("Server running on following IP addresses:");
        dumpIPs();
        System.err.println("Server running, press Ctrl-C to stop it.");
        try {
            synchronized (Main.class) {
                Main.class.wait();
            }
        } finally {
            server.shutdownNow();
        }
    }

    private static void turnLoggingOn() {
        ConsoleHandler ch = new ConsoleHandler();
        ch.setLevel(Level.ALL);
        Logger l = Logger.getLogger("org.glassfish.grizzly.http.server.HttpHandler");
        turnLoggingOn(l, ch);
        turnLoggingOn(LOG, ch);
    }

    private static void turnLoggingOn(Logger l, ConsoleHandler ch) {
        l.setLevel(Level.FINE);
        l.setUseParentHandlers(false);
        l.addHandler(ch);
    }

    static HttpServer createServer(URI u, File dir) {
        ResourceConfig rc = new ResourceConfig(
            TimingResource.class, ContactsResource.class,
            Main.class
        );
        final Storage storage = dir == null ? Storage.empty() : Storage.forDirectory(dir);
        final Settings settings = new Settings().withName("timings");
        rc.registerInstances(new AbstractBinder() {
            @Override
            protected void configure() {
                bind(storage).to(Storage.class);
                bind(settings).to(Settings.class);
            }
        });
        HttpServer server = GrizzlyHttpServerFactory.createHttpServer(u, rc);
        return server;
    }

    @Override
    public void filter(
        ContainerRequestContext requestContext,
        ContainerResponseContext r
    ) throws IOException {
        r.getHeaders().add("Access-Control-Allow-Origin", "*");
        r.getHeaders().add("Access-Control-Allow-Credentials", "true");
        r.getHeaders().add("Access-Control-Allow-Headers", "Content-Type");
        r.getHeaders().add("Access-Control-Allow-Methods", "GET, POST, DELETE, PUT");
    }

    private static void dumpIPs() throws Exception {
        Enumeration<NetworkInterface> en = NetworkInterface.getNetworkInterfaces();
        while (en.hasMoreElements()) {
            NetworkInterface n = en.nextElement();
            if (n.isUp()) {
                for (InterfaceAddress i : n.getInterfaceAddresses()) {
                    if (i.getAddress() instanceof Inet4Address) {
                        System.err.println(n.getName() + ": " + i.getAddress());
                    }
                }
            }
        }
    }
}
